telzo2000/cool943S/img/img008.jpg

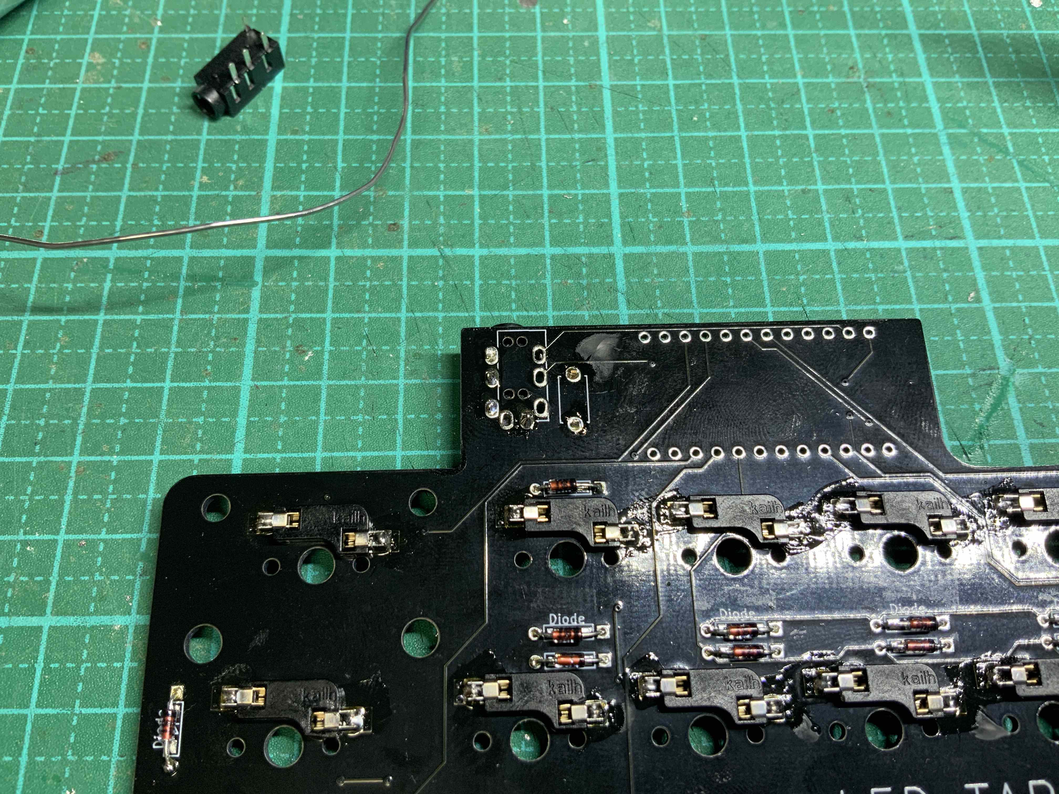
img/img008.jpg
