telzo2000/cool943S/img/img019.jpg

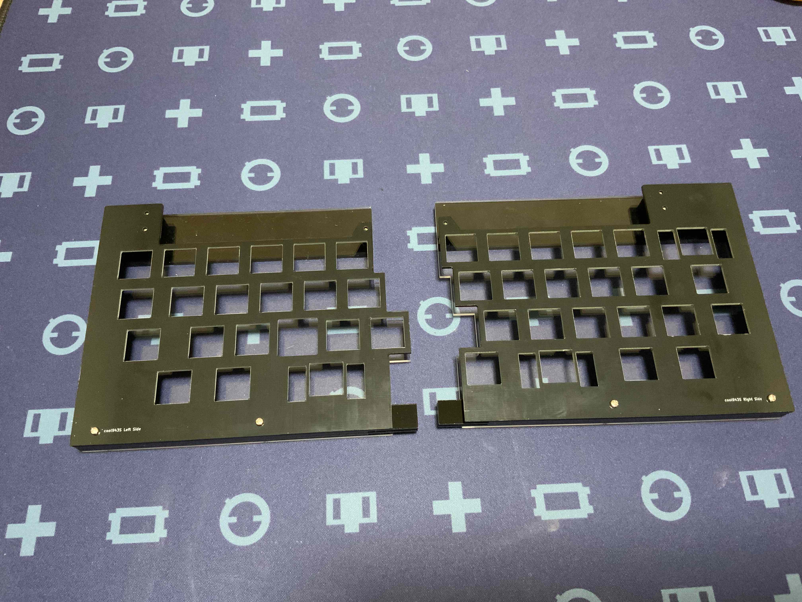
img/img019.jpg
