telzo2000/cool943S/img/img021.jpg

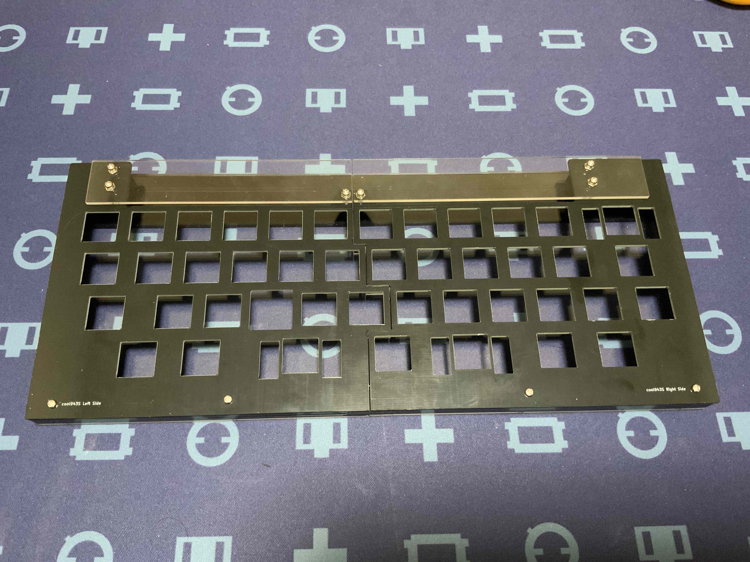
img/img021.jpg
